raptorlightning/I2S-Hat/I2SHat/Outputs/I2SHat_3D_Bottom.png

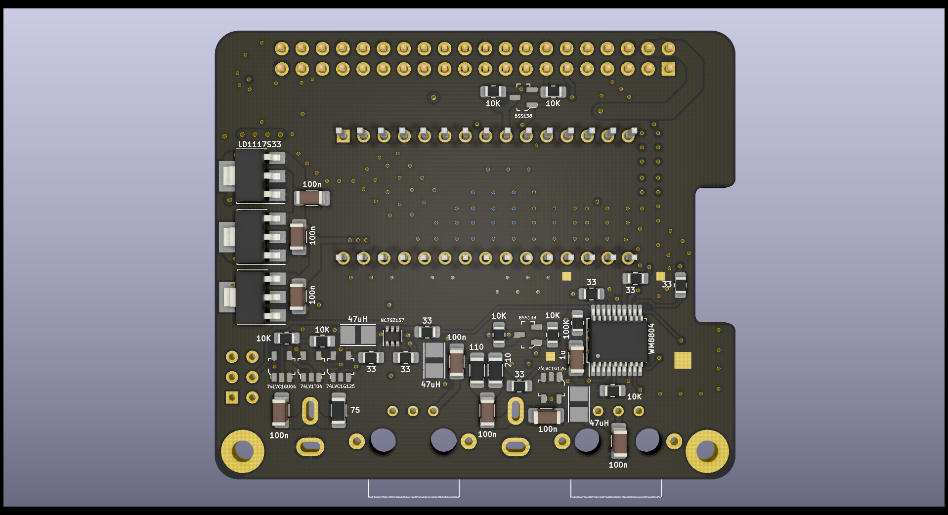
I2SHat/Outputs/I2SHat_3D_Bottom.png
